tonydero/dactyl-keyboard/things/test.scad

difference () {
  translate ([-56.27338164769888, 62.9565168793326, 8.8]) {
    cube ([10.5, 10.0, 17.6], center=true);
  }
  translate ([-56.27338164769888, 62.9565168793326, 8.8]) {
    cube ([6.5, 10.0, 13.6], center=true);
  }
}
